Rukenshia/pocketpuck/include/amp_logo.h

#pragma once

#include <Arduino.h>

constexpr int16_t AMP_LOGO_WIDTH = 230;
constexpr int16_t AMP_LOGO_HEIGHT = 118;

const uint16_t AMP_LOGO_ROW_OFFSETS[] PROGMEM = {
  0, 1, 2, 3, 4, 5, 6, 7, 8, 9, 10, 11,
  12, 13, 14, 15, 16, 19, 24, 39, 54, 69, 84, 99,
  114, 129, 142, 159, 176, 193, 210, 227, 244, 259, 274, 289,
  304, 319, 334, 349, 364, 379, 394, 409, 424, 439, 454, 469,
  484, 499, 514, 529, 544, 559, 574, 589, 604, 619, 634, 649,
  664, 679, 694, 709, 724, 739, 754, 769, 784, 799, 814, 829,
  844, 859, 874, 889, 904, 919, 934, 949, 966, 983, 1000, 1017,
  1034, 1047, 1062, 1077, 1092, 1107, 1122, 1137, 1152, 1159, 1166, 1169,
  1172, 1175, 1178, 1181, 1184, 1187, 1190, 1193, 1196, 1199, 1202, 1205,
  1208, 1211, 1214, 1217, 1220, 1223, 1226, 1229, 1232, 1235, 1238,
};

// Each row starts with a span count followed by inclusive x-start/x-end pairs.
const uint8_t AMP_LOGO_ROW_SPANS[] PROGMEM = {
  0x00, 0x00, 0x00, 0x00, 0x00, 0x00, 0x00, 0x00, 0x00, 0x00, 0x00, 0x00, 0x00, 0x00, 0x00, 0x00,
  0x01, 0xC0, 0xC2, 0x02, 0x1E, 0x2F, 0xB8, 0xCA, 0x07, 0x1A, 0x34, 0x49, 0x52, 0x5F, 0x68, 0x74,
  0x7C, 0x87, 0x90, 0x9E, 0xA7, 0xB4, 0xCD, 0x07, 0x18, 0x36, 0x48, 0x52, 0x5F, 0x69, 0x73, 0x7D,
  0x87, 0x91, 0x9D, 0xA7, 0xB1, 0xD0, 0x07, 0x15, 0x39, 0x48, 0x52, 0x5E, 0x69, 0x72, 0x7D, 0x87,
  0x91, 0x9D, 0xA7, 0xAF, 0xD2, 0x07, 0x14, 0x3A, 0x48, 0x52, 0x5E, 0x68, 0x72, 0x7C, 0x86, 0x91,
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
  0x4D, 0x59, 0x63, 0x6D, 0x77, 0x81, 0x8B, 0x98, 0xA2, 0xDB, 0xE5, 0x07, 0x00, 0x0B, 0x43, 0x4D,
  0x59, 0x63, 0x6D, 0x77, 0x81, 0x8B, 0x98, 0xA2, 0xDA, 0xE5, 0x07, 0x00, 0x0B, 0x43, 0x4D, 0x59,
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
};
