Rukenshia/pocketpuck/include/network_config.example.h

#pragma once

// Copy this file to include/network_config.h and fill in your local values.
// network_config.h is ignored by git so credentials are not committed.
#define POCKETPUCK_WIFI_SSID "your-wifi-name"
#define POCKETPUCK_WIFI_PASSWORD "your-wifi-password"
#define POCKETPUCK_STATS_URL "http://192.168.1.100:8765/stats"
